rhysfaultless/weather-station/software_raspberry_pi/testing_libraries/testing_time_rpi_os.py

import time

print ("/r")
print ("time.time_ns()")
print (time.time_ns())
print ("/r")
print ("/r")
print ("time.time()")
print (time.time())
print ("/r")
print ("/r")
print ("time.gmtime()")
print (time.gmtime())
print ("/r")
print ("/r")
print ("time.gmtime()[0]")
print (time.gmtime()[0])
print ("/r")
print ("/r")
